txp666/OTTO_ESP32/Firmware/Otto-ESP32-fw/include/anger1/images/anger1-6.png

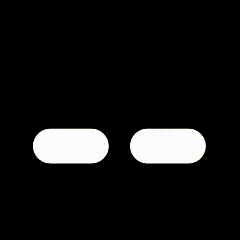
Firmware/Otto-ESP32-fw/include/anger1/images/anger1-6.png
