txp666/OTTO_ESP32/Firmware/Otto-ESP32-fw/include/excited/images/excited1_29.png

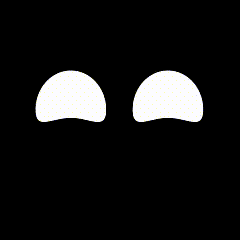
Firmware/Otto-ESP32-fw/include/excited/images/excited1_29.png
