txp666/OTTO_ESP32/Firmware/Otto-ESP32-fw/include/gif/disdain2.gif

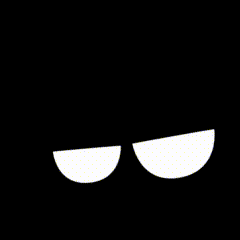
Firmware/Otto-ESP32-fw/include/gif/disdain2.gif
