txp666/OTTO_ESP32/Firmware/Otto-ESP32-fw/include/gif/Llook2.gif

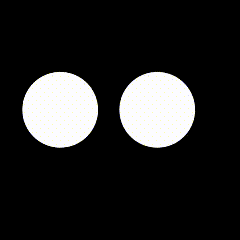
Firmware/Otto-ESP32-fw/include/gif/Llook2.gif
