txp666/OTTO_ESP32/Firmware/Otto-ESP32-fw/src/App/Configs/Config.h

#ifndef __CONFIG_H
#define __CONFIG_H

/*=========================
   Application configuration
 *=========================*/







/*=========================
   Hardware Configuration
 *=========================*/



/* Screen */

#define CONFIG_SCREEN_BLK_PIN       12

#define CONFIG_SCREEN_HOR_RES       240
#define CONFIG_SCREEN_VER_RES       240
#define CONFIG_SCREEN_BUFFER_SIZE   (CONFIG_SCREEN_HOR_RES * CONFIG_SCREEN_VER_RES /2)

/* Battery */
#define CONFIG_BAT_DET_PIN          37
#define CONFIG_BAT_CHG_DET_PIN      38

/* Buzzer */
#define CONFIG_BUZZ_PIN             25
#define CONFIG_BUZZ_CHANNEL         2
#define CONFIG_SOUND_ENABLE_DEFAULT true



/* SD CARD */
#define CONFIG_SD_SPI               SPI_SD
#define CONFIG_SD_CD_PIN            -1
#define CONFIG_SD_CS_PIN            15
#define CONFIG_SD_DET_PIN           22



#endif
